sphuro/Riscy/2025-05-09_13-59.png

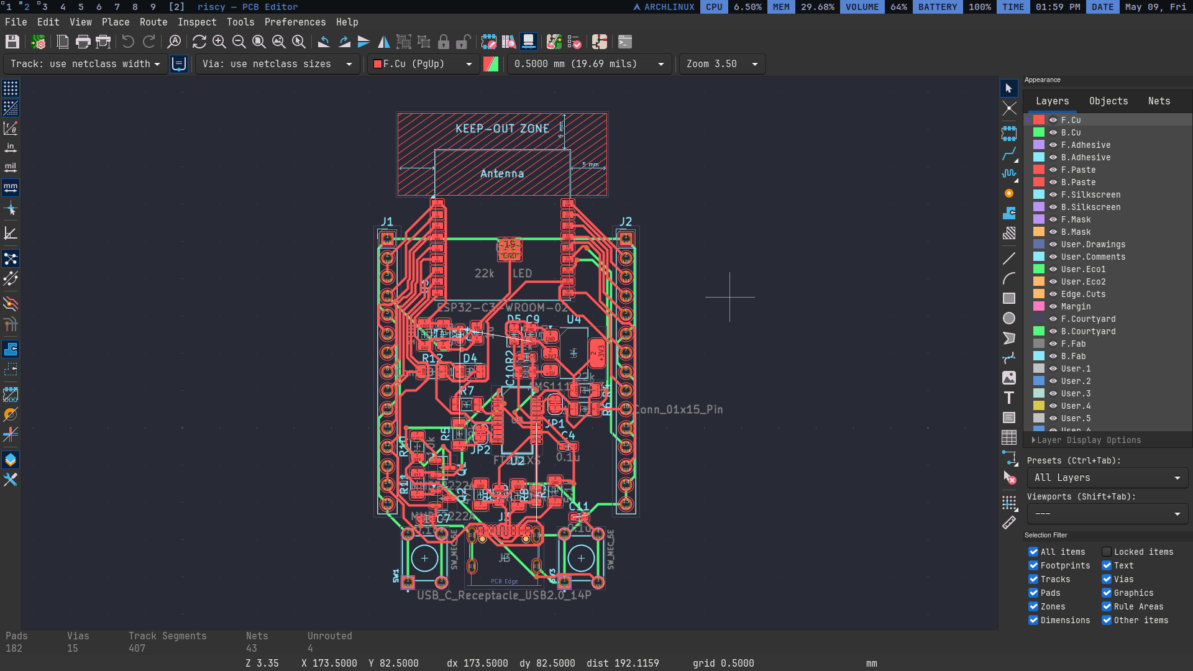
2025-05-09_13-59.png
